eagletrt/fenice-bms-hv-sw/Schematics/BMS_HV-2017-2018 chimera/BMS_HV/MainBoard/V1/MainBoard.kicad_pcb

## KiCad design Schematics/BMS_HV-2017-2018 chimera/BMS_HV/MainBoard/V1/MainBoard.kicad_pcb (2018-10-10, an earlier design)

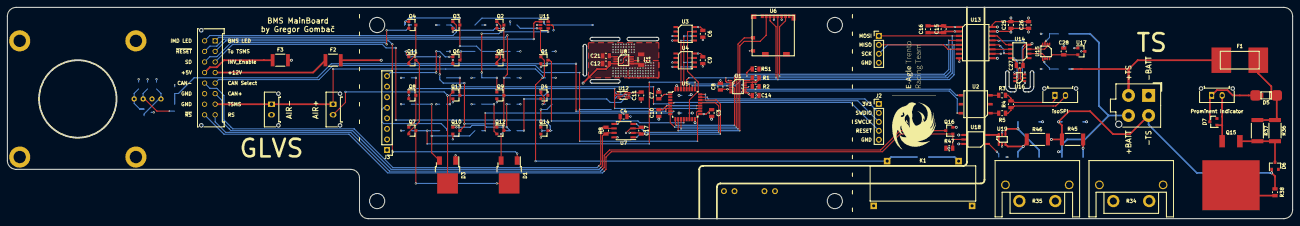
[picture p15: board MainBoard.kicad_pcb from above]

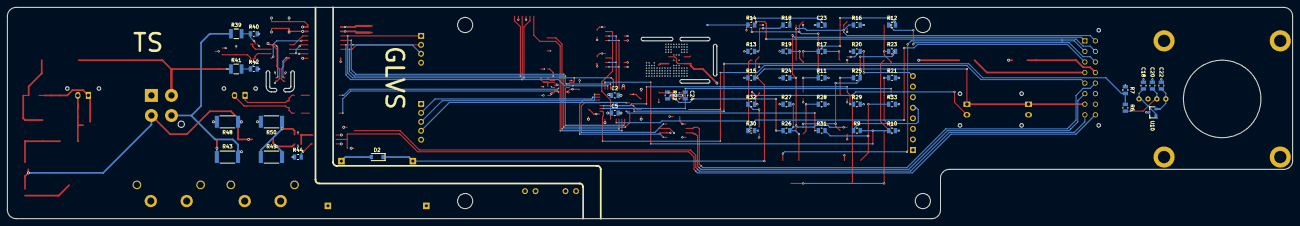
[picture p16: board MainBoard.kicad_pcb from below]

Board: 4 copper layers, 365.0 x 60.0 mm, 133 parts (45 on the bottom side), 98 nets.

Parts:
C1: 47u; C_1206_3216Metric
C2, C12: 4.7u; C_0805_2012Metric
C3, C4, C7, C11, C15, C17, C26, C28: 100n; C_0805_2012Metric
C5, C23, C27: 1u; C_0805_2012Metric
C6, C8, C9, C10, C14, C21, C24: 10n; C_0805_2012Metric
C16, C25: 10u; C_0805_2012Metric
C18, C22: 47n; C_0805_2012Metric
C20: 4.7n; C_0805_2012Metric
D1, D3: BT150S-600R; TO-252-2
D2: BAS16GW; D_SOD-123
D4, D6, D7: MMBZ4624; D_SOT-23_ANK
D5: BZD27C56P; DO-219AB
F1: 0885001.DR; SMD_Fuse
F2, F3: 0ZCG 2A; Fuse_1812_4532Metric
J1: isoSPI; Molex_Micro-Fit_3.0_43650-0215_1x02_P3.00mm_Vertical
J2: SWDebug; PinHeader_1x05_P2.54mm_Vertical
J3: IMD; PinHeader_1x08_P3mm_Vertical
J4: IO; Molex_Micro-Fit_3.0_43045-1612_2x08_P3.00mm_Vertical
J5: AIR-; Molex_Micro-Fit_3.0_43650-0215_1x02_P3.00mm_Vertical
J6: AIR+; Molex_Micro-Fit_3.0_43650-0215_1x02_P3.00mm_Vertical
J7: ProminentIndicator; Molex_Micro-Fit_3.0_43650-0215_1x02_P3.00mm_Vertical
J8: HV; Molex_Mega-Fit_76829-0104_2x02_P5.70mm_Vertical
J9: IMD_TS+; PinHeader_1x02_P3mm_Vertical
J10: IMD_TS-; PinHeader_1x02_P3mm_Vertical
K1: KT12-1A; KT_THT
Q1, Q5, Q6, Q12: TSM2306; SOT-23
Q2, Q3, Q4, Q7, Q9, Q10, Q11: TSM3401; SOT-23
Q8, Q13, Q16: TSM2312; SOT-23
Q14: BC846AW; SOT-23
Q15: BULB49D; D2PAK
R1: 604; R_0805_2012Metric
R2: 1.4K; R_0805_2012Metric
R3, R5: 22; R_0805_2012Metric
R4: 100; R_0805_2012Metric
R6, R7, R16, R17, R18, R19, R24, R25, R28: 10K; R_0805_2012Metric
R8: 120; R_0805_2012Metric
R9: 1.6K; R_0805_2012Metric
R10: 590; R_0805_2012Metric
R11, R14, R15, R21, R22, R27, R29, R33, R47: 100K; R_0805_2012Metric
R12, R23: 1M; R_0805_2012Metric
R13: 220K; R_0805_2012Metric
R20: 2K2; R_0805_2012Metric
R26, R31: 3.3K; R_0805_2012Metric
R30, R51: 1K; R_0805_2012Metric
R32: 22K; R_0805_2012Metric
R34, R35: 10K; TO-247_wHeatsink
R36, R37: 390K; R_2512_6332Metric
R38: 330; R_0805_2012Metric
R39, R41: 10M; R_1210_3225Metric
R40: 71K5; R_0805_2012Metric
R42: 34K8; R_0805_2012Metric
R43, R48: 100M; R_2512_6332Metric
R44: 470; R_0805_2012Metric
R45: 10M; R_2512_6332Metric
R46: 1G; R_2512_6332Metric
R49, R50: 2.2M; R_2512_6332Metric
U1: LTC6820; MSOP-16
U2: HM2103
U3, U4: M24M02; SON-8
U5: STM32F334K8; LQFP-32_7x7mm_P0.8mm
U6: MicroSD; Molex_MicroSD_PushPull
U7: MCP2562; SOIC-8_3.9x4.9mm_P1.27mm
U8: LP2989; SOIC-8
U9: HTFS200-P; HTFS 200-P
U10: REF2920; SOT-23
U11: MAX16053; SOT-23-6
U12: SN74LVC1G123; VSSOP-8_2.3x2mm_P0.5mm
U13: ISOW7841; SOIC-16
U14: LTC1865L; SON-8
U15: LTC6259; MSOP-8
U16: REF3433; SOT-23-6
U17: REF2940; SOT-23
U18: FODM611
U19: TPS3700; SOT-23-6

Connections:
+3V3: C1.1, C2.1, C3.1, C4.1, C5.1, C6.1, C7.1, C8.1, C9.1, C10.1, C11.1, C15.1, C16.1, J2.1, R14.1, R22.2, R51.2, U1.6, U3.8, U4.3, U4.8, U5.1, U5.5, U5.17, U6.4, U7.5, U8.5, U8.6, U12.3, U12.8, U13.1
+5V: C12.1, C14.1, C17.1, C18.1, F3.1, U1.9, U1.12, U7.3, U8.4, U8.8, U9.1, U10.1, U18.6
+12V: F2.2, J3.2, Q2.2, Q3.2, Q9.2, Q10.2, R11.1, R13.1, R16.2, R21.2, R24.2, R30.1, U11.5
+BATT: J8.4, K1.3, R39.2, R43.1
+TS: F1.1, J8.3, J9.1, J9.2, R34.2, R35.2, R41.2, R43.2, R45.1
-BATT: C25.2, C26.2, C27.2, C28.2, J8.1, R40.2, R42.2, R48.2, R50.1, U13.9, U13.15, U14.4, U15.4, U16.1, U16.2, U17.3, U19.2
-TS: D6.2, J8.2, J10.1, J10.2, R38.2, R45.2, R46.2, R48.1
/6820: U1.5, U5.9
/BMS_Fault: Q13.1, R29.1, U5.20
/CAN+: J4.6, R8.2, U7.7
/CAN-: J4.13, R8.1, U7.6
/CANS: J4.5, U5.18
/CD: U5.11, U6.9
/Current: C20.1, R6.1, U9.3
/HV/3V3ISO: C27.1, U14.8, U16.5, U16.6
/HV/4VISO: C28.1, U15.8, U17.2
/HV/5VISO: C25.1, C26.1, R44.1, U13.10, U13.16, U16.3, U16.4, U17.1, U19.5
/HV/PackV: U14.3, U15.1, U15.2
/HV/TSV: U14.2, U15.6, U15.7
/I+: U1.11, U2.4
/I-: U1.10, U2.6
/IBIAS: R1.2, U1.16
/ICMP: R1.1, R2.2, U1.15
/IMD: R9.2, R10.1, U5.25
/IMD_Fault: J3.8, Q6.1, R20.1
/MISO: R51.1, U1.3, U5.27, U6.7, U13.6
/MOSI: U1.2, U5.28, U6.3, U13.3
/PADC: U5.8, U13.4
/PC_Ended: R31.2, U5.7
/RST: J2.4, U5.4
/SCK: U1.4, U5.26, U6.5, U13.5
/SCL: U3.6, U4.6, U5.29
/SDA: U3.5, U4.5, U5.30
/SDCard: U5.10, U6.2
/SD_Status: Q1.3, U5.12
/SWCLK: J2.3, U5.24
/SWDIO: J2.2, U5.23
/Shutdown/BMS_SD: Q7.2, Q11.3
/Shutdown/IMD_SD: Q4.3, Q11.2, R23.2
/Shutdown/~RESET: Q2.1, Q9.1, R11.2, U11.4
/TS_ON: Q8.1, U5.19, U12.2
/WC: U3.7, U4.7, U5.14
/isoSPI+: J1.1, R3.1, R4.2
/isoSPI-: J1.2, R4.1, R5.1
BMS_LED: J4.1, Q9.3, Q10.1, Q12.3, R24.1
From_SD: J4.11, Q4.2, R12.2
From_TSMS: D2.1, J4.7, J5.1, J6.1, K1.1, Q1.1, R15.1
GND: C1.2, C2.2, C3.2, C4.2, C5.2, C6.2, C7.2, C8.2, C9.2, C10.2, C11.2, C12.2, C14.2, C15.2, C16.2, C17.2, C18.2, C20.2, C21.2, C22.2, C23.2, D2.2, D3.1, J2.5, J3.1, J3.3, J3.4, J4.14, J4.15, J5.2, K1.2, Q1.2, Q6.2, Q8.2, Q13.2, Q14.2, Q16.2, R2.1, R7.1, R10.2, R15.2, R18.2, R19.1, R20.2, R27.2, R28.1, R29.2, R33.2, R47.2, U1.1, U1.7, U1.8, U1.13, U1.14, U3.3, U3.4, U4.4, U5.16, U5.31, U5.32, U6.6, U6.10, U7.2, U7.8, U8.3, U9.2, U10.3, U11.2, U12.1, U12.4, U13.2, U13.8, U18.4
IMD_LED: J4.9, Q2.3, Q3.1, Q5.3, R16.1
INV_Enable: J4.3, Q14.3, R30.2
NRelayStat: J4.16, Q16.1, R47.1, U18.5
unnamed: C21.1, U8.1
unnamed: C22.1, U9.4, U10.2
unnamed: C23.1, U11.6
unnamed: C24.1, R22.1, U12.7
unnamed: C24.2, U12.6
unnamed: D1.2, Q7.3
unnamed: D1.3, R26.1, R27.1
unnamed: D3.2, D4.1, J6.2
unnamed: D3.3, R31.1, R33.1
unnamed: D4.2, R32.2
unnamed: D5.1, D7.1, J7.1
unnamed: D5.2, F1.2, R36.1, R37.1
unnamed: D6.1, Q15.1, R36.2, R37.2
unnamed: D7.2, J7.2, Q15.2
unnamed: F2.1, J4.4
unnamed: F3.2, J4.12
unnamed: J3.5, R9.1
unnamed: K1.4, R34.1, R35.1
unnamed: Q3.3, Q4.1, Q5.1, R12.1, R17.1
unnamed: Q5.2, R19.2
unnamed: Q6.3, R17.2
unnamed: Q7.1, Q8.3, R21.1
unnamed: Q10.3, Q11.1, Q12.1, R23.1, R25.1
unnamed: Q12.2, R28.2
unnamed: Q13.3, R25.2
unnamed: Q14.1, R32.1
unnamed: Q15.3, R38.1
unnamed: R3.2, U2.3
unnamed: R5.2, U2.1
unnamed: R6.2, R7.2, U5.6
unnamed: R13.2, R18.1, U11.3
unnamed: R26.2, U12.5
unnamed: R39.1, R40.1, U15.3
unnamed: R41.1, R42.1, U15.5
unnamed: R44.2, U18.1
unnamed: R46.1, R49.1, U19.3
unnamed: R49.2, R50.2, U19.4
unnamed: U5.21, U7.4
unnamed: U5.22, U7.1
unnamed: U13.11, U14.6
unnamed: U13.12, U14.7
unnamed: U13.13, U14.1
unnamed: U13.14, U14.5
unnamed: U18.3, U19.1, U19.6
RESET_BUTTON: J4.10, R14.2, U11.1
RelayStat: J4.8, Q16.3
To_TSMS: D1.1, J4.2
