eagletrt/fenice-bms-hv-sw/openblt_cellboard/Core/Inc/main.h

#define ADDRESS_2_Pin GPIO_PIN_1
#define ADDRESS_2_GPIO_Port GPIOA
#define ADDRESS_1_Pin GPIO_PIN_2
#define ADDRESS_1_GPIO_Port GPIOA
#define ADDRESS_0_Pin GPIO_PIN_3
#define ADDRESS_0_GPIO_Port GPIOA
#define LED_Pin GPIO_PIN_15
#define LED_GPIO_Port GPIOA
