eagletrt/fenice-bms-hv-sw/mainboard/Src/pack/current.c

/**
 * @file current.c
 * @brief Functions that handle current measurement
 *
 * @date Sep 24, 2021
 *
 * @author Matteo Bonora [matteo.bonora@studenti.unitn.it]
 * @author Federico Carbone [federico.carbone@studenti.unitn.it]
 * @author Antonio Gelain [antonio.gelain@studenti.unitn.it]
 */
#include "pack/current.h"

#include <math.h>
#include <stdbool.h>

#include "stm32f4xx_hal.h"
#include "mainboard_config.h"
#include "error_simple.h"

#define MEASURE_SAMPLE_SIZE 128

#define CURRENT_SENSITIVITY_LOW 40e-3f // V / A
#define CURRENT_SENSITIVITY_HIGH 6.67e-3f // V / A

#define CURRENT_DIVIDER_RATIO_INVERSE ((330.f + 169.f) / 330.f)

uint16_t adc_50[MEASURE_SAMPLE_SIZE]  = { 0 };
uint16_t adc_300[MEASURE_SAMPLE_SIZE] = { 0 };

current_t prev_current = 0.f, filtered_current = 0.f;
current_t current[CURRENT_SENSOR_NUM] = { 0.f };

current_t V0L = 0, V0H = 0;  // Voltage offset (Vout(0A))
current_t volt_300 = 0; // Voltage value of the Hall effect sensor

current_t _current_convert_low(float volt) {
    return (CURRENT_DIVIDER_RATIO_INVERSE / CURRENT_SENSITIVITY_LOW) * (volt - V0L);
}

current_t _current_convert_high(float volt) {
    return (CURRENT_DIVIDER_RATIO_INVERSE / CURRENT_SENSITIVITY_HIGH) * (volt - V0H);
}

#define CURRENT_SHUNT_VREF_OFFSET 0.454f // 0.9f
#define CURRENT_SHUNT_OP_GAIN 75.f
#define CURRENT_SHUNT_RESISTANCE 1e-4f

current_t _current_convert_shunt(float volt) {
    return (volt - CURRENT_SHUNT_VREF_OFFSET) / (CURRENT_SHUNT_OP_GAIN * CURRENT_SHUNT_RESISTANCE);
}

void current_start_measure() {
    HAL_ADC_Start_DMA(&ADC_HALL50, (uint32_t *)adc_50, MEASURE_SAMPLE_SIZE);
    HAL_ADC_Start_DMA(&ADC_HALL300, (uint32_t *)adc_300, MEASURE_SAMPLE_SIZE);
}


uint32_t current_read(float shunt_adc_val) {
    uint32_t time = HAL_GetTick();
    float avg_50 = 0;
    float avg_300 = 0;
    for (size_t i = 0; i < MEASURE_SAMPLE_SIZE; i++) {
        avg_50 += adc_50[i];
        avg_300 += adc_300[i];
    }

    // Convert Hall-low (50A)
    float volt = avg_50 * 3.3f / 4095.f / MEASURE_SAMPLE_SIZE;
    current[CURRENT_SENSOR_50] = _current_convert_low(volt);

    // Convert Hall-high (300A)
    volt_300 = avg_300 * 3.3f / 4095.f / MEASURE_SAMPLE_SIZE;
    current[CURRENT_SENSOR_300] = _current_convert_high(volt_300);

    // Convert Shunt
    current[CURRENT_SENSOR_SHUNT] = _current_convert_shunt(shunt_adc_val);

    // Filter current
    current_t hall_50 = fabsf(current[CURRENT_SENSOR_50]);
    current_t hall_300 = fabsf(current[CURRENT_SENSOR_300]);

    // Return current read from the correct
    if (hall_50 < 34 && hall_300 < 34)
        filtered_current = current[CURRENT_SENSOR_50];
    else
        filtered_current = current[CURRENT_SENSOR_300];
    // Filter current
    const float alpha = 0.4f;
    prev_current = filtered_current = alpha * prev_current + (1.f - alpha) * filtered_current;

    // Check for over-currents
    if (current_get_current() < CURRENT_MIN_THRESHOLD) {
        error_simple_set(ERROR_GROUP_ERROR_OVER_CURRENT, 0);
    } else {
        error_simple_reset(ERROR_GROUP_ERROR_OVER_CURRENT, 0);
    }

    if (current_get_current() > CURRENT_MAX_THRESHOLD) {
        error_simple_set(ERROR_GROUP_ERROR_OVER_CURRENT, 0);
    } else {
        error_simple_reset(ERROR_GROUP_ERROR_OVER_CURRENT, 0);
    }
    return time;
}

void current_zero() {
    uint32_t avg_50  = 0;
    uint32_t avg_300 = 0;
    for (size_t i = 0; i < MEASURE_SAMPLE_SIZE; ++i) {
        avg_50 += adc_50[i];
        avg_300 += adc_300[i];
    }
    V0L = avg_50 * (3.3f / 4095 / MEASURE_SAMPLE_SIZE);
    V0H = avg_300 * (3.3f / 4095 / MEASURE_SAMPLE_SIZE);
}

current_t current_get_current() {
    return filtered_current;
}
current_t * current_get_current_sensors() {
    return current;
}

current_t current_get_current_from_sensor(uint8_t sensor) {
    if (sensor >= CURRENT_SENSOR_NUM)
        return 0;
    return current[sensor];
}

void current_check_errors() {
    current_t hall_300 = current[CURRENT_SENSOR_300];
    if (hall_300 < CURRENT_MIN_THRESHOLD) {
        error_simple_set(ERROR_GROUP_ERROR_OVER_CURRENT, 0);
    } else {
        error_simple_reset(ERROR_GROUP_ERROR_OVER_CURRENT, 0);
    }

    if (hall_300 > CURRENT_MAX_THRESHOLD) {
        error_simple_set(ERROR_GROUP_ERROR_OVER_CURRENT, 0);
    } else {
        error_simple_reset(ERROR_GROUP_ERROR_OVER_CURRENT, 0);
    }
    
    // Hall effect sensor disconnected
    if (volt_300 < CURRENT_SENSOR_DISCONNECTED_THRESHOLD) {
        // error_simple_set(ERROR_GROUP_ERROR_CONNECTOR_DISCONNECTED, 1);
    } else {
        error_simple_reset(ERROR_GROUP_ERROR_CONNECTOR_DISCONNECTED, 1);
    }
}
