eagletrt/fenice-bms-hv-sw/openblt_cellboard/Core/Inc/BLT/blt_conf.h

/************************************************************************************//**
* \file         Demo/ARMCM4_STM32F4_Nucleo_F429ZI_GCC/Boot/blt_conf.h
* \brief        Bootloader configuration header file.
* \ingroup      Boot_ARMCM4_STM32F4_Nucleo_F429ZI_GCC
* \internal
*----------------------------------------------------------------------------------------
*                          C O P Y R I G H T
*----------------------------------------------------------------------------------------
*   Copyright (c) 2021  by Feaser    http://www.feaser.com    All rights reserved
*
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
* OpenBLT is distributed in the hope that it will be useful, but WITHOUT ANY WARRANTY;
* without even the implied warranty of MERCHANTABILITY or FITNESS FOR A PARTICULAR
* PURPOSE. See the GNU General Public License for more details.
*
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
* \endinternal
****************************************************************************************/
#ifndef BLT_CONF_H
#define BLT_CONF_H

#include "main.h"

/****************************************************************************************
*   C P U   D R I V E R   C O N F I G U R A T I O N
****************************************************************************************/
/* To properly initialize the baudrate clocks of the communication interface, typically
 * the speed of the crystal oscillator and/or the speed at which the system runs is
 * needed. Set these through configurables BOOT_CPU_XTAL_SPEED_KHZ and
 * BOOT_CPU_SYSTEM_SPEED_KHZ, respectively. To enable data exchange with the host that is
 * not dependent on the targets architecture, the byte ordering needs to be known.
 * Setting BOOT_CPU_BYTE_ORDER_MOTOROLA to 1 selects big endian mode and 0 selects
 * little endian mode.
 *
 * Set BOOT_CPU_USER_PROGRAM_START_HOOK to 1 if you would like a hook function to be
 * called the moment the user program is about to be started. This could be used to
 * de-initialize application specific parts, for example to stop blinking an LED, etc.
 */
/** \brief Frequency of the external crystal oscillator. */
#define BOOT_CPU_XTAL_SPEED_KHZ          (20000)
/** \brief Desired system speed. */
#define BOOT_CPU_SYSTEM_SPEED_KHZ        (80000)
/** \brief Motorola or Intel style byte ordering. */
#define BOOT_CPU_BYTE_ORDER_MOTOROLA     (0)
/** \brief Enable/disable hook function call right before user program start. */
#define BOOT_CPU_USER_PROGRAM_START_HOOK (0)


/****************************************************************************************
*   C O M M U N I C A T I O N   I N T E R F A C E   C O N F I G U R A T I O N
****************************************************************************************/
/* The NET communication interface for firmware updates via TCP/IP is selected by setting
 * the BOOT_COM_NET_ENABLE configurable to 1. The maximum amount of data bytes in a
 * message for data transmission and reception is set through BOOT_COM_NET_TX_MAX_DATA
 * and BOOT_COM_NET_RX_MAX_DATA, respectively. The default IP address is configured
 * with the macros BOOT_COM_NET_IPADDRx. The default netmask is configured with the
 * macro BOOT_COM_NET_NETMASKx. The default gateway is configured with the macros
 * BOOT_COM_NET_GATEWAYx. The bootloader acts and a TCP/IP server. The port the server
 * listen on for connections is configured with BOOT_COM_NET_PORT.
 * In case the network switch/router supports a DHCP server, you can set configuration
 * macro BOOT_COM_NET_DHCP_ENABLE to 1 to enable the DHCP client. In this case the
 * DHCP client handles the automatic IP address assignment. In this case the macros for
 * configuring the IP address, network mask and gateway address are no longer needed.
 */
/** \brief Enable/disable the NET transport layer. */
#define BOOT_COM_NET_ENABLE               (0)
/** \brief Configure number of bytes in the target->host data packet. */
#define BOOT_COM_NET_TX_MAX_DATA          (64)
/** \brief Configure number of bytes in the host->target data packet. */
#define BOOT_COM_NET_RX_MAX_DATA          (64)
/** \brief Configure the port that the TCP/IP server listens on */
#define BOOT_COM_NET_PORT                 (1000)
/** \brief Enable/disable DHCP client for automatically obtaining an IP address. */
#define BOOT_COM_NET_DHCP_ENABLE          (1)
/** \brief Configure the 1st byte of the IP address */
#define BOOT_COM_NET_IPADDR0              (192)
/** \brief Configure the 2nd byte of the IP address */
#define BOOT_COM_NET_IPADDR1              (168)
/** \brief Configure the 3rd byte of the IP address */
#define BOOT_COM_NET_IPADDR2              (178)
/** \brief Configure the 4th byte of the IP address */
#define BOOT_COM_NET_IPADDR3              (50)
/** \brief Configure the 1st byte of the network mask */
#define BOOT_COM_NET_NETMASK0             (255)
/** \brief Configure the 2nd byte of the network mask */
#define BOOT_COM_NET_NETMASK1             (255)
/** \brief Configure the 3rd byte of the network mask */
#define BOOT_COM_NET_NETMASK2             (255)
/** \brief Configure the 4th byte of the network mask */
#define BOOT_COM_NET_NETMASK3             (0)
/** \brief Configure the 1st byte of the gateway address */
#define BOOT_COM_NET_GATEWAY0             (192)
/** \brief Configure the 2nd byte of the gateway address */
#define BOOT_COM_NET_GATEWAY1             (168)
/** \brief Configure the 3rd byte of the gateway address */
#define BOOT_COM_NET_GATEWAY2             (178)
/** \brief Configure the 4th byte of the gateway address */
#define BOOT_COM_NET_GATEWAY3             (1)
/** \brief Enable/disable the deferred initialization mechanism. When enabled, the
 *         communication interface is only initialized when: (a) no valid user program
 *         is detected, or (b) when CpuUserProgramStartHook() returns BLT_FALSE. Your
 *         bootloader application can explicitly initialize the communication interface
 *         by calling ComDeferredInit().
 */
#define BOOT_COM_NET_DEFERRED_INIT_ENABLE (1)

/* The USB communication interface is selected by setting the BOOT_COM_USB_ENABLE
 * configurable to 1. The maximum amount of data bytes in a message for data transmission
 * and reception is set through BOOT_COM_USB_TX_MAX_DATA and BOOT_COM_USB_RX_MAX_DATA,
 * respectively.
 *
 */
/** \brief Enable/disable USB transport layer. */
#define BOOT_COM_USB_ENABLE             (0)
/** \brief Configure number of bytes in the target->host data packet. */
#define BOOT_COM_USB_TX_MAX_DATA        (63)
/** \brief Configure number of bytes in the host->target data packet. */
#define BOOT_COM_USB_RX_MAX_DATA        (63)

/* The CAN communication interface is selected by setting the BOOT_COM_CAN_ENABLE
 * configurable to 1. Configurable BOOT_COM_CAN_BAUDRATE selects the communication speed
 * in bits/second. Two CAN messages are reserved for communication with the host. The
 * message identifier for sending data from the target to the host is configured with
 * BOOT_COM_CAN_TXMSG_ID. The one for receiving data from the host is configured with
 * BOOT_COM_CAN_RXMSG_ID. Note that an extended 29-bit CAN identifier is configured by
 * OR-ing with mask 0x80000000. The maximum amount of data bytes in a message for data
 * transmission and reception is set through BOOT_COM_CAN_TX_MAX_DATA and
 * BOOT_COM_CAN_RX_MAX_DATA, respectively. It is common for a microcontroller to have more
 * than 1 CAN controller on board. The zero-based BOOT_COM_CAN_CHANNEL_INDEX selects the
 * CAN controller channel.
 *
 */
/** \brief Enable/disable CAN transport layer. */
#define BOOT_COM_CAN_ENABLE             (1)
/** \brief Configure the desired CAN baudrate. */
#define BOOT_COM_CAN_BAUDRATE           (1000000)
/** \brief Configure CAN message ID target->host. */
#define BOOT_COM_CAN_TX_MSG_ID          (0x04 + 2 * (HAL_GPIO_ReadPin(ADDRESS_2_GPIO_Port, ADDRESS_2_Pin) | HAL_GPIO_ReadPin(ADDRESS_1_GPIO_Port, ADDRESS_1_Pin) << 1 | HAL_GPIO_ReadPin(ADDRESS_0_GPIO_Port, ADDRESS_0_Pin) << 2))
/** \brief Configure number of bytes in the target->host CAN message. */
#define BOOT_COM_CAN_TX_MAX_DATA        (8)
/** \brief Configure CAN message ID host->target. */
#define BOOT_COM_CAN_RX_MSG_ID          (0x05 + 2 * (HAL_GPIO_ReadPin(ADDRESS_2_GPIO_Port, ADDRESS_2_Pin) | HAL_GPIO_ReadPin(ADDRESS_1_GPIO_Port, ADDRESS_1_Pin) << 1 | HAL_GPIO_ReadPin(ADDRESS_0_GPIO_Port, ADDRESS_0_Pin) << 2))
/** \brief Configure number of bytes in the host->target CAN message. */
#define BOOT_COM_CAN_RX_MAX_DATA        (8)
/** \brief Select the desired CAN peripheral as a zero based index. */
#define BOOT_COM_CAN_CHANNEL_INDEX      (0)

/* The RS232 communication interface is selected by setting the BOOT_COM_RS232_ENABLE
 * configurable to 1. Configurable BOOT_COM_RS232_BAUDRATE selects the communication speed
 * in bits/second. The maximum amount of data bytes in a message for data transmission
 * and reception is set through BOOT_COM_RS232_TX_MAX_DATA and BOOT_COM_RS232_RX_MAX_DATA,
 * respectively. It is common for a microcontroller to have more than 1 UART interface
 * on board. The zero-based BOOT_COM_RS232_CHANNEL_INDEX selects the UART interface.
 *
 */
/** \brief Enable/disable UART transport layer. */
#define BOOT_COM_RS232_ENABLE            (0)
/** \brief Configure the desired communication speed. */
#define BOOT_COM_RS232_BAUDRATE          (57600)
/** \brief Configure number of bytes in the target->host data packet. */
#define BOOT_COM_RS232_TX_MAX_DATA       (64)
/** \brief Configure number of bytes in the host->target data packet. */
#define BOOT_COM_RS232_RX_MAX_DATA       (64)
/** \brief Select the desired UART peripheral as a zero based index. */
#define BOOT_COM_RS232_CHANNEL_INDEX     (2)


/****************************************************************************************
*   B A C K D O O R   E N T R Y   C O N F I G U R A T I O N
****************************************************************************************/
/* It is possible to implement an application specific method to force the bootloader to
 * stay active after a reset. Such a backdoor entry into the bootloader is desired in
 * situations where the user program does not run properly and therefore cannot
 * reactivate the bootloader. By enabling these hook functions, the application can
 * implement the backdoor, which overrides the default backdoor entry that is programmed
 * into the bootloader. When desired for security purposes, these hook functions can
 * also be implemented in a way that disables the backdoor entry altogether.
 */
/** \brief Enable/disable the backdoor override hook functions. */
#define BOOT_BACKDOOR_HOOKS_ENABLE      (0)

/** \brief Backdoor timeout before starting user program */
#define BOOT_BACKDOOR_ENTRY_TIMEOUT_MS (1000)

/****************************************************************************************
*   N O N - V O L A T I L E   M E M O R Y   D R I V E R   C O N F I G U R A T I O N
****************************************************************************************/
/* The NVM driver typically supports erase and program operations of the internal memory
 * present on the microcontroller. Through these hook functions the NVM driver can be
 * extended to support additional memory types such as external flash memory and serial
 * eeproms. The size of the internal memory in kilobytes is specified with configurable
 * BOOT_NVM_SIZE_KB. If desired the internal checksum writing and verification method can
 * be overridden with a application specific method by enabling configuration switch
 * BOOT_NVM_CHECKSUM_HOOKS_ENABLE.
 */
/** \brief Enable/disable the NVM hook function for supporting additional memory devices. */
#define BOOT_NVM_HOOKS_ENABLE           (0)
/** \brief Configure the size of the default memory device (typically flash EEPROM). */
#define BOOT_NVM_SIZE_KB                (128)
/** \brief Enable/disable hooks functions to override the user program checksum handling. */
#define BOOT_NVM_CHECKSUM_HOOKS_ENABLE  (0)


/****************************************************************************************
*   F L A S H   M E M O R Y   D R I V E R   C O N F I G U R A T I O N
****************************************************************************************/
/** \brief This microcontroller has a larger vector table then the default STM32F7xx
 *         project as assumed in the bootloader's core. This means the user program has
 *         a different checksum location, because this one is added at the end of the
 *         user program's vector table.
 */
#define BOOT_FLASH_VECTOR_TABLE_CS_OFFSET (0x194)


/****************************************************************************************
*   W A T C H D O G   D R I V E R   C O N F I G U R A T I O N
****************************************************************************************/
/* The COP driver cannot be configured internally in the bootloader, because its use
 * and configuration is application specific. The bootloader does need to service the
 * watchdog in case it is used. When the application requires the use of a watchdog,
 * set BOOT_COP_HOOKS_ENABLE to be able to initialize and service the watchdog through
 * hook functions.
 */
/** \brief Enable/disable the hook functions for controlling the watchdog. */
#define BOOT_COP_HOOKS_ENABLE           (0)


/****************************************************************************************
*   S E E D / K E Y   S E C U R I T Y   C O N F I G U R A T I O N
****************************************************************************************/
/* A security mechanism can be enabled in the bootloader's XCP module by setting configu-
 * rable BOOT_XCP_SEED_KEY_ENABLE to 1. Before any memory erase or programming
 * operations can be performed, access to this resource need to be unlocked.
 * In the Microboot settings on tab "XCP Protection" you need to specify a DLL that
 * implements the unlocking algorithm. The demo programs are configured for the (simple)
 * algorithm in "libseednkey.dll". The source code for this DLL is available so it can be
 * customized to your needs.
 * During the unlock sequence, Microboot requests a seed from the bootloader, which is in
 * the format of a byte array. Using this seed the unlock algorithm in the DLL computes
 * a key, which is also a byte array, and sends this back to the bootloader. The
 * bootloader then verifies this key to determine if programming and erase operations are
 * permitted.
 * After enabling this feature the hook functions XcpGetSeedHook() and XcpVerifyKeyHook()
 * are called by the bootloader to obtain the seed and to verify the key, respectively.
 */
#define BOOT_XCP_SEED_KEY_ENABLE        (0)


#endif /* BLT_CONF_H */
/*********************************** end of blt_conf.h *********************************/
