eagletrt/fenice-bms-hv-sw/src/bms/Src/ltc6813.c

/**
 * @file		ltc6813.c
 * @brief		This file contains the functions to communicate with the LTCs
 *
 * @date		Oct 08, 2019
 * @author	Matteo Bonora [matteo.bonora@studenti.unitn.it]
 */

#include "ltc6813.h"

// Set to 1 to emulate the LTC daisy chain
#define LTC6813_EMU 0

/**
 * @brief		Polls all the registers of the LTC6813 and updates the cell
 * array
 * @details	It executes multiple rdcv requests to the LTCs and saves the values
 * 					in the voltage variable of the CELL_Ts.
 *
 * 					1     CMD0    8     CMD1      16      32
 * 					|- - - - - - -|- - - - - - - -|- ... -|
 * 					1 0 0 0 0 0 0 0 0 0 0 0 X X X X  PEC
 * 					 Address |             |  Reg  |
 * 					  (BRD)
 *
 * @param		spi		The SPI configuration structure
 * @param		ltc		The array of LTC6813 configurations
 * @param		volts	The array of voltages
 * @param		error	The error return value
 */
uint8_t ltc6813_read_voltages(SPI_HandleTypeDef *spi, LTC6813_T ltc[],
							  uint16_t volts[], ERROR_STATUS_T volts_error[],
							  WARNING_T *warning, ERROR_T *error) {
	uint8_t cmd[4];
	uint16_t cmd_pec;
	uint8_t data[8];

	cmd[0] = 0;  // Broadcast

	uint8_t count = 0;  // volts[] index
	for (uint8_t reg = 0; reg < LTC6813_REG_COUNT; reg++) {
		cmd[1] = (uint8_t)rdcv_cmd[reg];
		cmd_pec = _pec15(2, cmd);
		cmd[2] = (uint8_t)(cmd_pec >> 8);
		cmd[3] = (uint8_t)(cmd_pec);

		_wakeup_idle(spi, false);

		HAL_GPIO_WritePin(CS_LTC_GPIO_Port, CS_LTC_Pin, GPIO_PIN_RESET);
		if (HAL_SPI_Transmit(spi, cmd, 4, 100) != HAL_OK) {
			// goto End;
		}
		HAL_SPI_Receive(spi, data, 8 * LTC6813_COUNT, 100);
		HAL_GPIO_WritePin(CS_LTC_GPIO_Port, CS_LTC_Pin, GPIO_PIN_SET);

#if LTC6813_EMU > 0
		// Writes 3.6v to each cell

		uint8_t emu_i;
		for (emu_i = 0; emu_i < LTC6813_REG_CELL_COUNT * 2; emu_i++) {
			// 36000
			data[emu_i] = 0b10100000;
			data[++emu_i] = 0b10001100;
		}
		uint16_t emu_pec = _pec15(6, data);
		data[6] = (uint8_t)(emu_pec >> 8);
		data[7] = (uint8_t)emu_pec;
#endif

		if (_pec15(6, data) == (uint16_t)(data[6] * 256 + data[7])) {
			error_unset(ERROR_LTC_PEC_ERROR, &ltc->error);

			// For every cell in the register
			for (uint8_t cell = 0; cell < LTC6813_REG_CELL_COUNT; cell++) {
				volts[count] = _convert_voltage(&data[2 * cell]);

				ltc6813_check_voltage(volts[count], &volts_error[count],
									  warning, error);
				ER_CHK(error);
				count++;
			}
		} else {
			error_set(ERROR_LTC_PEC_ERROR, &ltc->error, HAL_GetTick());
		}

		*error = error_check_fatal(&ltc->error, HAL_GetTick());
		ER_CHK(error);
	}

End:;
	return count;
}

/**
 * @brief		Starts the LTC6813 ADC voltage conversion
 * @details	According to the datasheet, this command should take 2,335µs.
 * 					ADCV Command syntax:
 *
 * 					1     CMD0    8     CMD1      16      32
 * 					|- - - - - - -|- - - - - - - -|- ... -|
 * 					0 0 0 0 0 0 1 1 0 1 1 X 0 0 0 0  PEC
 * 					 Address |    | |     |
 * 					  (BRD)      Speed   DCP
 *
 * @param		spi		The spi configuration structure
 * @param		dcp		false to read voltages; true to read temperatures
 */
void _ltc6813_adcv(SPI_HandleTypeDef *spi, bool dcp) {
	uint8_t cmd[4];
	uint16_t cmd_pec;
	cmd[0] = (uint8_t)0b00000011;
	cmd[1] = (uint8_t)0b01100000 + dcp * 0b00010000;
	cmd_pec = _pec15(2, cmd);
	cmd[2] = (uint8_t)(cmd_pec >> 8);
	cmd[3] = (uint8_t)(cmd_pec);

	_wakeup_idle(spi, false);
	HAL_GPIO_WritePin(CS_LTC_GPIO_Port, CS_LTC_Pin, GPIO_PIN_RESET);
	HAL_SPI_Transmit(spi, cmd, 4, 100);
	HAL_Delay(1);
	HAL_GPIO_WritePin(CS_LTC_GPIO_Port, CS_LTC_Pin, GPIO_PIN_SET);
}

/**
 * @brief		Enable or disable the temperature measurement through
 *balancing
 * @details	Since it's not possible to read the temperatures from adiacent
 * 					cells at the same time, We split the measurement into
 *two times, read odd cells, and then even ones. To write configuration you
 *have to send 2 consecutive commands:
 *
 *					WRCFG:
 * 					1     CMD0    8     CMD1      16      32
 * 					|- - - - - - -|- - - - - - - -|- ... -|
 * 					0 0 0 0 0 0 0 0 0 0 0 0 0 0 0 1  PEC
 *
 *					CFGR:
 * 					1             8               16
 * 					|- - - - - - -|- - - - - - - -|
 * 					0 0 0 0 0 0 0 0 0 0 0 0 0 0 0 0
 * 					17            24              32
 * 					|- - - - - - -|- - - - - - - -|
 * 					0 0 0 0 0 0 0 0 0 0 0 0 0 0 0 0
 *					33            40              48      64
 *					|- - - - - - -|- - - - - - - -|- ... -|
 *					1 0 0 1 0 1 0 1 0 0 0 0 0 0 1 0  PEC	<- For odd cells
 *					              or
 *					0 1 0 0 1 0 1 0 0 0 0 0 0 0 0 1  PEC	<- For even
 *cells
 *
 * @param		hspi			The SPI configuration structure
 * @param		start_bal	whether to start temperature measurement
 * @param		even			Indicates whether we're reading odd or even
 *cells
 */
// TODO: remove this function
void _ltc6813_wrcfg(SPI_HandleTypeDef *hspi, bool start_bal, bool even) {
	uint8_t wrcfg[4];
	uint8_t cfgr[8];

	uint16_t cmd_pec;

	wrcfg[0] = 0x00;
	wrcfg[1] = 0x01;
	cmd_pec = _pec15(2, wrcfg);
	wrcfg[2] = (uint8_t)(cmd_pec >> 8);
	wrcfg[3] = (uint8_t)(cmd_pec);

	cfgr[0] = 0x00;
	cfgr[1] = 0x00;
	cfgr[2] = 0x00;
	cfgr[3] = 0x00;

	if (start_bal) {
		if (even) {
			// Command to balance cells (in order) 8,5,3,1 and 10
			cfgr[4] = 0b10010101;
			cfgr[5] = 0b00000010;
		} else {
			// Command to balance cells (in order) 7,4,2 and 9
			cfgr[4] = 0b01001010;
			// First 4 bits are for DCT0 and should remain 0
			cfgr[5] = 0b00000001;
		}
	} else {
		cfgr[4] = 0x00;
		cfgr[5] = 0x00;
	}
	cmd_pec = _pec15(6, cfgr);
	cfgr[6] = (uint8_t)(cmd_pec >> 8);
	cfgr[7] = (uint8_t)(cmd_pec);

	_wakeup_idle(hspi, true);

	HAL_GPIO_WritePin(CS_LTC_GPIO_Port, CS_LTC_Pin, GPIO_PIN_RESET);
	HAL_SPI_Transmit(hspi, wrcfg, 4, 100);
	HAL_Delay(1);
	HAL_SPI_Transmit(hspi, cfgr, 8, 100);
	HAL_Delay(1);
	HAL_GPIO_WritePin(CS_LTC_GPIO_Port, CS_LTC_Pin, GPIO_PIN_SET);

	// TODO: remove this
	_ltc6813_adcv(hspi, start_bal);
}

/**
 * @brief		This function is used to fetch the temperatures.
 * @details	The workings of this function are very similar to read_voltages,
 * 					the main difference to it is the presence of the even
 * 					parameter. Refer to the ltc6813_read_voltages comment for
 * 					the actual messages.
 *
 * @param		hspi		The SPI configuration structure
 * @param		even		indicates which set of cells is currently being
 * 									balanced: false for odd and true for even
 * cells
 * @param		ltc			The array of LTC6813 configurations
 * @param		temps		The array of temperatures
 * @param		error		The error return value
 */
uint8_t ltc6813_read_temperatures(SPI_HandleTypeDef *hspi, LTC6813_T *ltc,
								  uint16_t temps[],
								  ERROR_STATUS_T temps_error[],
								  ERROR_T *error) {
	uint8_t cmd[4];
	uint16_t cmd_pec;
	uint8_t data[8];

	cmd[0] = (uint8_t)0x80 + ltc->address;

	uint8_t count = 0;
	for (uint8_t reg = 0; reg < LTC6813_REG_COUNT; reg++) {
		cmd[1] = (uint8_t)rdcv_cmd[reg];
		cmd_pec = _pec15(2, cmd);
		cmd[2] = (uint8_t)(cmd_pec >> 8);
		cmd[3] = (uint8_t)(cmd_pec);

		_wakeup_idle(hspi, false);

		HAL_GPIO_WritePin(CS_LTC_GPIO_Port, CS_LTC_Pin, GPIO_PIN_RESET);
		HAL_Delay(1);
		HAL_SPI_Transmit(hspi, cmd, 4, 100);

		HAL_SPI_Receive(hspi, data, 8, 100);
		HAL_Delay(1);
		HAL_GPIO_WritePin(CS_LTC_GPIO_Port, CS_LTC_Pin, GPIO_PIN_SET);

#if LTC6813_EMU > 0
		// Writes 0.9292v (18°C) to each sensor

		for (uint8_t emu_i = 0; emu_i < LTC6813_REG_CELL_COUNT * 2; emu_i++) {
			// 9292
			data[emu_i] = 0b00100100;
			data[++emu_i] = 0b01001100;
		}
		uint16_t emu_pec = _pec15(6, data);
		data[6] = (uint8_t)(emu_pec >> 8);
		data[7] = (uint8_t)emu_pec;
#endif

		if (_pec15(6, data) == (uint16_t)(data[6] * 256 + data[7])) {
			error_unset(ERROR_LTC_PEC_ERROR, &ltc->error);

			// Counts the cell inside the register
			for (uint8_t cell = 0; cell < LTC6813_REG_CELL_COUNT; cell++) {
				uint16_t temp =
					_convert_temp(_convert_voltage(&data[2 * cell]));

				if (temp > 0) {
					temps[count] = temp;

					ltc6813_check_temperature(temps[count], &temps_error[count],
											  error);
					ER_CHK(error);
				}

				count++;
			}
		} else {
			error_set(ERROR_LTC_PEC_ERROR, &ltc->error, HAL_GetTick());
		}
	}

	*error = error_check_fatal(&ltc->error, HAL_GetTick());
	ER_CHK(error);  // In case of error, set the error and goto label End

End:;

	return count;
}

void ltc6813_wrcfg(SPI_HandleTypeDef *hspi, bool is_a,
				   uint8_t cfgr[LTC6813_COUNT][8]) {
	uint8_t cmd[4] = {0};

	if (is_a) {
		// WRCFGA
		cmd[1] = 1;
	} else {
		// WRCFGB
		cmd[1] = 0b00100100;
	}

	uint16_t cmd_pec = _pec15(2, cmd);
	cmd[2] = (uint8_t)(cmd_pec >> 8);
	cmd[3] = (uint8_t)(cmd_pec);

	HAL_GPIO_WritePin(CS_LTC_GPIO_Port, CS_LTC_Pin, GPIO_PIN_RESET);
	HAL_SPI_Transmit(hspi, cmd, 4, 100);
	HAL_Delay(1);

	for (uint8_t i = 0; i < LTC6813_COUNT; i++) {
		HAL_SPI_Transmit(hspi, cfgr[i], 8, 100);
	}

	HAL_GPIO_WritePin(CS_LTC_GPIO_Port, CS_LTC_Pin, GPIO_PIN_SET);
}

void _set_dcc(uint8_t indexes[], uint8_t cfgar[8], uint8_t cfgbr[8]) {
	for (uint8_t i = 0; i < PACK_MODULE_COUNT; i++) {
		if (indexes[i] < 8) {
			cfgar[4] += dcc[indexes[i]];
		} else if (indexes[i] >= 8 && indexes[i] < 12) {
			cfgar[5] += dcc[indexes[i]];
		} else if (indexes[i] >= 12 && indexes[i] < 16) {
			cfgbr[0] += dcc[indexes[i]];
		} else if (indexes[i] >= 16 && indexes[i] < 18) {
			cfgbr[1] += dcc[indexes[i]];
		}

		uint16_t pec = _pec15(6, cfgar);
		cfgar[6] = (uint8_t)(pec >> 8);
		cfgar[7] = (uint8_t)(pec);

		pec = _pec15(6, cfgbr);
		cfgbr[6] = (uint8_t)(pec >> 8);
		cfgbr[7] = (uint8_t)(pec);
	}
}

void ltc6813_set_balancing(SPI_HandleTypeDef *hspi, uint8_t *indexes,
						   int dcto) {
	uint8_t cfgar[LTC6813_COUNT][8] = {0};
	uint8_t cfgbr[LTC6813_COUNT][8] = {0};

	for (uint8_t i = 0; i < LTC6813_COUNT; i++) {
		// cfgbr[i][1] += 0b00001000; // set DTMEN
		cfgar[i][0] += 0b00000010;  // set DTEN
		cfgar[i][5] += dcto << 4;   // Set timer

		// For each LTC we set the correct cfgr
		_set_dcc(indexes, cfgar[i], cfgbr[i]);
	}
	_wakeup_idle(hspi, true);

	ltc6813_wrcfg(hspi, true, cfgar);
	ltc6813_wrcfg(hspi, false, cfgbr);
}

void ltc6813_wrcomm_i2c(SPI_HandleTypeDef *hspi, uint8_t data[1]) {
	uint8_t cmd[4] = {0b00000111, 0b00100001};  // WRCOMM

	uint16_t cmd_pec = _pec15(2, cmd);
	cmd[2] = (uint8_t)(cmd_pec >> 8);
	cmd[3] = (uint8_t)(cmd_pec);

	uint8_t comm[8];
	comm[0] = I2C_START & (data[0] >> 4);
	comm[1] = (data[0] << 4) & I2C_MASTER_ACK;

	comm[2] = I2C_BLANK & (data[1] >> 4);
	comm[3] = (data[1] << 4) & I2C_MASTER_ACK;

	comm[4] = I2C_STOP & (data[2] >> 4);
	comm[5] = (data[2] << 4) & I2C_MASTER_ACK;

	uint16_t pec = _pec15(6, comm);
	comm[6] = (uint8_t)(pec >> 8);
	comm[7] = (uint8_t)(pec);

	HAL_GPIO_WritePin(CS_LTC_GPIO_Port, CS_LTC_Pin, GPIO_PIN_RESET);
	HAL_SPI_Transmit(hspi, cmd, 4, 100);
	HAL_Delay(1);

	HAL_SPI_Transmit(hspi, comm, 8, 100);

	HAL_GPIO_WritePin(CS_LTC_GPIO_Port, CS_LTC_Pin, GPIO_PIN_SET);
}

void ltc6813_stcomm_i2c(SPI_HandleTypeDef *hspi) {
	uint8_t cmd[4] = {0};  // WRCOMM

	cmd[0] = 0b00000111;
	cmd[1] = 0b00100011;

	uint16_t cmd_pec = _pec15(2, cmd);
	cmd[2] = (uint8_t)(cmd_pec >> 8);
	cmd[3] = (uint8_t)(cmd_pec);

	HAL_GPIO_WritePin(CS_LTC_GPIO_Port, CS_LTC_Pin, GPIO_PIN_RESET);
	HAL_SPI_Transmit(hspi, cmd, 4, 100);
	HAL_SPI_Receive(hspi, NULL, 3 * 8 * 3, 200);
	HAL_GPIO_WritePin(CS_LTC_GPIO_Port, CS_LTC_Pin, GPIO_PIN_SET);
}

/**
 * @brief		Checks that voltage is between its thresholds.
 *
 * @param		volts		The voltage
 * @param		error		The error return code
 */
void ltc6813_check_voltage(uint16_t volts, ERROR_STATUS_T *volt_error,
						   WARNING_T *warning, ERROR_T *error) {
	if (volts < CELL_WARN_VOLTAGE) {
		*warning = WARN_CELL_LOW_VOLTAGE;
	}

	if (volts < CELL_MIN_VOLTAGE) {
		error_set(ERROR_CELL_UNDER_VOLTAGE, volt_error, HAL_GetTick());
	} else {
		error_unset(ERROR_CELL_UNDER_VOLTAGE, volt_error);
	}

	if (volts > CELL_MAX_VOLTAGE) {
		error_set(ERROR_CELL_OVER_VOLTAGE, volt_error, HAL_GetTick());
	} else {
		error_unset(ERROR_CELL_OVER_VOLTAGE, volt_error);
	}

	*error = error_check_fatal(volt_error, HAL_GetTick());
	ER_CHK(error);

End:;
}

/**
 * @brief		Checks that temperature is between its thresholds.
 *
 * @param		temp		The temperature
 * @param		error		The error return code
 */
void ltc6813_check_temperature(uint16_t temps, ERROR_STATUS_T *temp_error,
							   ERROR_T *error) {
	if (temps >= CELL_MAX_TEMPERATURE) {
		error_set(ERROR_CELL_OVER_TEMPERATURE, temp_error, HAL_GetTick());
	} else {
		error_unset(ERROR_CELL_OVER_TEMPERATURE, temp_error);
	}

	*error = error_check_fatal(temp_error, HAL_GetTick());
	ER_CHK(error);

End:;
}

/**
 * @brief		Wakes up all the devices connected to the isoSPI bus
 *
 * @param		hspi	The SPI configuration structure
 */
void _wakeup_idle(SPI_HandleTypeDef *hspi, bool apply_delay) {
	uint8_t data = 0xFF;
	HAL_GPIO_WritePin(CS_LTC_GPIO_Port, CS_LTC_Pin, GPIO_PIN_RESET);
	HAL_SPI_Transmit(hspi, &data, 1, 1);
	if (apply_delay) {
		HAL_Delay(1);
	}
	HAL_GPIO_WritePin(CS_LTC_GPIO_Port, CS_LTC_Pin, GPIO_PIN_SET);
}

/**
 * @brief		This function is used to calculate the PEC value
 *
 * @param		len		Length of the data array
 * @param		data	Array of data
 */
uint16_t _pec15(uint8_t len, uint8_t data[]) {
	uint16_t remainder, address;
	remainder = 16;  // PEC seed
	for (int i = 0; i < len; i++) {
		// calculate PEC table address
		address = ((remainder >> 7) ^ data[i]) & 0xff;
		remainder = (remainder << 8) ^ crcTable[address];
	}
	// The CRC15 has a 0 in the LSB so the final value must be multiplied by 2
	return (remainder * 2);
}

/**
 * @brief	This function is used to convert the 2 byte raw data from the
 * 				LTC68xx to a 16 bit unsigned integer
 *
 * @param 	v_data	Raw data bytes
 *
 * @retval	Voltage [mV]
 */
uint16_t _convert_voltage(uint8_t v_data[]) {
	return v_data[0] + (v_data[1] << 8);
}

/**
 * @brief		This function converts a voltage data from the zener sensor
 * 					to a temperature
 *
 * @param		volt	Voltage [mV]
 *
 * @retval	Temperature [C° * 100]
 */
uint16_t _convert_temp(uint16_t volt) {
	float voltf = volt * 0.0001;
	float temp;
	temp = -225.7 * voltf * voltf * voltf + 1310.6 * voltf * voltf -
		   2594.8 * voltf + 1767.8;
	return (uint16_t)(temp * 100);
}
