eagletrt/fenice-bms-hv-sw/mainboard/Src/can.c

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
/* Includes ------------------------------------------------------------------*/
#include "can.h"

/* USER CODE BEGIN 0 */

#define bms_IMPLEMENTATION
#define bms_IDS_IMPLEMENTATION
#define primary_IMPLEMENTATION
#define primary_IDS_IMPLEMENTATION

#include "can-bms.h"
#include "can-primary.h"

#undef bms_IMPLEMENTATION
#undef bms_IDS_IMPLEMENTATION
#undef primary_IMPLEMENTATION
#undef primary_IDS_IMPLEMENTATION

void MX_CAN1_Init_250K(void);
void MX_CAN1_Init_1M(void);

/* USER CODE END 0 */

CAN_HandleTypeDef hcan1;
CAN_HandleTypeDef hcan2;

/* CAN1 init function */
void MX_CAN1_Init(void) {
    hcan1.Instance                  = CAN1;
    hcan1.Init.Prescaler            = 3;
    hcan1.Init.Mode                 = CAN_MODE_NORMAL;
    hcan1.Init.SyncJumpWidth        = CAN_SJW_1TQ;
    hcan1.Init.TimeSeg1             = CAN_BS1_12TQ;
    hcan1.Init.TimeSeg2             = CAN_BS2_2TQ;
    hcan1.Init.TimeTriggeredMode    = DISABLE;
    hcan1.Init.AutoBusOff           = ENABLE;
    hcan1.Init.AutoWakeUp           = DISABLE;
    hcan1.Init.AutoRetransmission   = DISABLE;
    hcan1.Init.ReceiveFifoLocked    = DISABLE;
    hcan1.Init.TransmitFifoPriority = DISABLE;
    if (HAL_CAN_Init(&hcan1) != HAL_OK) {
        Error_Handler();
    }
}
/* CAN2 init function */
void MX_CAN2_Init(void) {
    hcan2.Instance                  = CAN2;
    hcan2.Init.Prescaler            = 3;
    hcan2.Init.Mode                 = CAN_MODE_NORMAL;
    hcan2.Init.SyncJumpWidth        = CAN_SJW_1TQ;
    hcan2.Init.TimeSeg1             = CAN_BS1_12TQ;
    hcan2.Init.TimeSeg2             = CAN_BS2_2TQ;
    hcan2.Init.TimeTriggeredMode    = DISABLE;
    hcan2.Init.AutoBusOff           = ENABLE;
    hcan2.Init.AutoWakeUp           = DISABLE;
    hcan2.Init.AutoRetransmission   = DISABLE;
    hcan2.Init.ReceiveFifoLocked    = DISABLE;
    hcan2.Init.TransmitFifoPriority = DISABLE;
    if (HAL_CAN_Init(&hcan2) != HAL_OK) {
        Error_Handler();
    }
}

static uint32_t HAL_RCC_CAN1_CLK_ENABLED = 0;

void HAL_CAN_MspInit(CAN_HandleTypeDef *canHandle) {
    GPIO_InitTypeDef GPIO_InitStruct = {0};
    if (canHandle->Instance == CAN1) {
        /* CAN1 clock enable */
        HAL_RCC_CAN1_CLK_ENABLED++;
        if (HAL_RCC_CAN1_CLK_ENABLED == 1) {
            __HAL_RCC_CAN1_CLK_ENABLE();
        }

        __HAL_RCC_GPIOA_CLK_ENABLE();
        /**CAN1 GPIO Configuration
    PA11     ------> CAN1_RX
    PA12     ------> CAN1_TX
    */
        GPIO_InitStruct.Pin       = CAN_CAR_RX_Pin | CAN_CAR_TX_Pin;
        GPIO_InitStruct.Mode      = GPIO_MODE_AF_PP;
        GPIO_InitStruct.Pull      = GPIO_NOPULL;
        GPIO_InitStruct.Speed     = GPIO_SPEED_FREQ_VERY_HIGH;
        GPIO_InitStruct.Alternate = GPIO_AF9_CAN1;
        HAL_GPIO_Init(GPIOA, &GPIO_InitStruct);

        /* CAN1 interrupt Init */
        HAL_NVIC_SetPriority(CAN1_RX0_IRQn, 0, 0);
        HAL_NVIC_EnableIRQ(CAN1_RX0_IRQn);
        HAL_NVIC_SetPriority(CAN1_RX1_IRQn, 0, 0);
        HAL_NVIC_EnableIRQ(CAN1_RX1_IRQn);
        HAL_NVIC_SetPriority(CAN1_SCE_IRQn, 0, 0);
        HAL_NVIC_EnableIRQ(CAN1_SCE_IRQn);
    } else if (canHandle->Instance == CAN2) {
        /* CAN2 clock enable */
        __HAL_RCC_CAN2_CLK_ENABLE();
        HAL_RCC_CAN1_CLK_ENABLED++;
        if (HAL_RCC_CAN1_CLK_ENABLED == 1) {
            __HAL_RCC_CAN1_CLK_ENABLE();
        }

        __HAL_RCC_GPIOB_CLK_ENABLE();
        /**CAN2 GPIO Configuration
    PB5     ------> CAN2_RX
    PB6     ------> CAN2_TX
    */
        GPIO_InitStruct.Pin       = CAN_CELL_RX_Pin | CAN_CELL_TX_Pin;
        GPIO_InitStruct.Mode      = GPIO_MODE_AF_PP;
        GPIO_InitStruct.Pull      = GPIO_NOPULL;
        GPIO_InitStruct.Speed     = GPIO_SPEED_FREQ_VERY_HIGH;
        GPIO_InitStruct.Alternate = GPIO_AF9_CAN2;
        HAL_GPIO_Init(GPIOB, &GPIO_InitStruct);

        /* CAN2 interrupt Init */
        HAL_NVIC_SetPriority(CAN2_RX0_IRQn, 0, 0);
        HAL_NVIC_EnableIRQ(CAN2_RX0_IRQn);
        HAL_NVIC_SetPriority(CAN2_RX1_IRQn, 0, 0);
        HAL_NVIC_EnableIRQ(CAN2_RX1_IRQn);
        HAL_NVIC_SetPriority(CAN2_SCE_IRQn, 0, 0);
        HAL_NVIC_EnableIRQ(CAN2_SCE_IRQn);
    }
}

void HAL_CAN_MspDeInit(CAN_HandleTypeDef *canHandle) {
    if (canHandle->Instance == CAN1) {
        /* Peripheral clock disable */
        HAL_RCC_CAN1_CLK_ENABLED--;
        if (HAL_RCC_CAN1_CLK_ENABLED == 0) {
            __HAL_RCC_CAN1_CLK_DISABLE();
        }

        /**CAN1 GPIO Configuration
    PA11     ------> CAN1_RX
    PA12     ------> CAN1_TX
    */
        HAL_GPIO_DeInit(GPIOA, CAN_CAR_RX_Pin | CAN_CAR_TX_Pin);

        /* CAN1 interrupt Deinit */
        HAL_NVIC_DisableIRQ(CAN1_RX0_IRQn);
        HAL_NVIC_DisableIRQ(CAN1_RX1_IRQn);
        HAL_NVIC_DisableIRQ(CAN1_SCE_IRQn);
    } else if (canHandle->Instance == CAN2) {
        /* Peripheral clock disable */
        __HAL_RCC_CAN2_CLK_DISABLE();
        HAL_RCC_CAN1_CLK_ENABLED--;
        if (HAL_RCC_CAN1_CLK_ENABLED == 0) {
            __HAL_RCC_CAN1_CLK_DISABLE();
        }

        /**CAN2 GPIO Configuration
    PB5     ------> CAN2_RX
    PB6     ------> CAN2_TX
    */
        HAL_GPIO_DeInit(GPIOB, CAN_CELL_RX_Pin | CAN_CELL_TX_Pin);

        /* CAN2 interrupt Deinit */
        HAL_NVIC_DisableIRQ(CAN2_RX0_IRQn);
        HAL_NVIC_DisableIRQ(CAN2_RX1_IRQn);
        HAL_NVIC_DisableIRQ(CAN2_SCE_IRQn);
    }
}

/* USER CODE BEGIN 1 */

void MX_CAN1_Init_250K(void) {
    hcan1.Instance                  = CAN1;
    hcan1.Init.Prescaler            = 10;
    hcan1.Init.Mode                 = CAN_MODE_NORMAL;
    hcan1.Init.SyncJumpWidth        = CAN_SJW_1TQ;
    hcan1.Init.TimeSeg1             = CAN_BS1_15TQ;
    hcan1.Init.TimeSeg2             = CAN_BS2_2TQ;
    hcan1.Init.TimeTriggeredMode    = DISABLE;
    hcan1.Init.AutoBusOff           = ENABLE;
    hcan1.Init.AutoWakeUp           = DISABLE;
    hcan1.Init.AutoRetransmission   = DISABLE;
    hcan1.Init.ReceiveFifoLocked    = DISABLE;
    hcan1.Init.TransmitFifoPriority = DISABLE;
    if (HAL_CAN_Init(&hcan1) != HAL_OK) {
        Error_Handler();
    }
}

void MX_CAN1_Init_1M(void) {
    hcan1.Instance                  = CAN1;
    hcan1.Init.Prescaler            = 3;
    hcan1.Init.Mode                 = CAN_MODE_NORMAL;
    hcan1.Init.SyncJumpWidth        = CAN_SJW_1TQ;
    hcan1.Init.TimeSeg1             = CAN_BS1_12TQ;
    hcan1.Init.TimeSeg2             = CAN_BS2_2TQ;
    hcan1.Init.TimeTriggeredMode    = DISABLE;
    hcan1.Init.AutoBusOff           = ENABLE;
    hcan1.Init.AutoWakeUp           = DISABLE;
    hcan1.Init.AutoRetransmission   = DISABLE;
    hcan1.Init.ReceiveFifoLocked    = DISABLE;
    hcan1.Init.TransmitFifoPriority = DISABLE;
    if (HAL_CAN_Init(&hcan1) != HAL_OK) {
        Error_Handler();
    }
}

/* USER CODE END 1 */
