eagletrt/fenice-bms-hv-sw/mainboard/Src/spi.c

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
/* Includes ------------------------------------------------------------------*/
#include "spi.h"

/* USER CODE BEGIN 0 */
void spi_enable_cs(SPI_HandleTypeDef *spi, GPIO_TypeDef *gpio, uint16_t pin) {
    HAL_GPIO_WritePin(gpio, pin, GPIO_PIN_RESET);
    while (spi->State != HAL_SPI_STATE_READY)
        ;
}

void spi_disable_cs(SPI_HandleTypeDef *spi, GPIO_TypeDef *gpio, uint16_t pin) {
    while (spi->State != HAL_SPI_STATE_READY)
        ;
    HAL_GPIO_WritePin(gpio, pin, GPIO_PIN_SET);
}
/* USER CODE END 0 */

SPI_HandleTypeDef hspi1;
SPI_HandleTypeDef hspi2;
SPI_HandleTypeDef hspi3;

/* SPI1 init function */
void MX_SPI1_Init(void)
{

  hspi1.Instance = SPI1;
  hspi1.Init.Mode = SPI_MODE_MASTER;
  hspi1.Init.Direction = SPI_DIRECTION_2LINES;
  hspi1.Init.DataSize = SPI_DATASIZE_8BIT;
  hspi1.Init.CLKPolarity = SPI_POLARITY_LOW;
  hspi1.Init.CLKPhase = SPI_PHASE_1EDGE;
  hspi1.Init.NSS = SPI_NSS_SOFT;
  hspi1.Init.BaudRatePrescaler = SPI_BAUDRATEPRESCALER_16;
  hspi1.Init.FirstBit = SPI_FIRSTBIT_MSB;
  hspi1.Init.TIMode = SPI_TIMODE_DISABLE;
  hspi1.Init.CRCCalculation = SPI_CRCCALCULATION_DISABLE;
  hspi1.Init.CRCPolynomial = 10;
  if (HAL_SPI_Init(&hspi1) != HAL_OK)
  {
    Error_Handler();
  }
}
/* SPI2 init function */
void MX_SPI2_Init(void)
{

  hspi2.Instance = SPI2;
  hspi2.Init.Mode = SPI_MODE_MASTER;
  hspi2.Init.Direction = SPI_DIRECTION_2LINES;
  hspi2.Init.DataSize = SPI_DATASIZE_8BIT;
  hspi2.Init.CLKPolarity = SPI_POLARITY_LOW;
  hspi2.Init.CLKPhase = SPI_PHASE_1EDGE;
  hspi2.Init.NSS = SPI_NSS_SOFT;
  hspi2.Init.BaudRatePrescaler = SPI_BAUDRATEPRESCALER_64;
  hspi2.Init.FirstBit = SPI_FIRSTBIT_MSB;
  hspi2.Init.TIMode = SPI_TIMODE_DISABLE;
  hspi2.Init.CRCCalculation = SPI_CRCCALCULATION_DISABLE;
  hspi2.Init.CRCPolynomial = 10;
  if (HAL_SPI_Init(&hspi2) != HAL_OK)
  {
    Error_Handler();
  }
}
/* SPI3 init function */
void MX_SPI3_Init(void)
{

  hspi3.Instance = SPI3;
  hspi3.Init.Mode = SPI_MODE_MASTER;
  hspi3.Init.Direction = SPI_DIRECTION_2LINES;
  hspi3.Init.DataSize = SPI_DATASIZE_8BIT;
  hspi3.Init.CLKPolarity = SPI_POLARITY_LOW;
  hspi3.Init.CLKPhase = SPI_PHASE_2EDGE;
  hspi3.Init.NSS = SPI_NSS_SOFT;
  hspi3.Init.BaudRatePrescaler = SPI_BAUDRATEPRESCALER_64;
  hspi3.Init.FirstBit = SPI_FIRSTBIT_MSB;
  hspi3.Init.TIMode = SPI_TIMODE_DISABLE;
  hspi3.Init.CRCCalculation = SPI_CRCCALCULATION_DISABLE;
  hspi3.Init.CRCPolynomial = 10;
  if (HAL_SPI_Init(&hspi3) != HAL_OK)
  {
    Error_Handler();
  }
}

void HAL_SPI_MspInit(SPI_HandleTypeDef* spiHandle)
{

  GPIO_InitTypeDef GPIO_InitStruct = {0};
  if(spiHandle->Instance==SPI1)
  {
    /* SPI1 clock enable */
    __HAL_RCC_SPI1_CLK_ENABLE();

    __HAL_RCC_GPIOA_CLK_ENABLE();
    /**SPI1 GPIO Configuration
    PA5     ------> SPI1_SCK
    PA6     ------> SPI1_MISO
    PA7     ------> SPI1_MOSI
    */
    GPIO_InitStruct.Pin = ADC_SCK_Pin|ADC_MISO_Pin|ADC_MOSI_Pin;
    GPIO_InitStruct.Mode = GPIO_MODE_AF_PP;
    GPIO_InitStruct.Pull = GPIO_NOPULL;
    GPIO_InitStruct.Speed = GPIO_SPEED_FREQ_VERY_HIGH;
    GPIO_InitStruct.Alternate = GPIO_AF5_SPI1;
    HAL_GPIO_Init(GPIOA, &GPIO_InitStruct);

  }
  else if(spiHandle->Instance==SPI2)
  {
    /* SPI2 clock enable */
    __HAL_RCC_SPI2_CLK_ENABLE();

    __HAL_RCC_GPIOB_CLK_ENABLE();
    /**SPI2 GPIO Configuration
    PB13     ------> SPI2_SCK
    PB14     ------> SPI2_MISO
    PB15     ------> SPI2_MOSI
    */
    GPIO_InitStruct.Pin = EEPROM_SCK_Pin|EEPROM_MISO_Pin|EEPROM_MOSI_Pin;
    GPIO_InitStruct.Mode = GPIO_MODE_AF_PP;
    GPIO_InitStruct.Pull = GPIO_NOPULL;
    GPIO_InitStruct.Speed = GPIO_SPEED_FREQ_VERY_HIGH;
    GPIO_InitStruct.Alternate = GPIO_AF5_SPI2;
    HAL_GPIO_Init(GPIOB, &GPIO_InitStruct);

  }
  else if(spiHandle->Instance==SPI3)
  {
    /* SPI3 clock enable */
    __HAL_RCC_SPI3_CLK_ENABLE();

    __HAL_RCC_GPIOC_CLK_ENABLE();
    __HAL_RCC_GPIOB_CLK_ENABLE();
    /**SPI3 GPIO Configuration
    PC11     ------> SPI3_MISO
    PC12     ------> SPI3_MOSI
    PB3     ------> SPI3_SCK
    */
    GPIO_InitStruct.Pin = MONITOR_MISO_Pin|MONITOR_MOSI_Pin;
    GPIO_InitStruct.Mode = GPIO_MODE_AF_PP;
    GPIO_InitStruct.Pull = GPIO_NOPULL;
    GPIO_InitStruct.Speed = GPIO_SPEED_FREQ_VERY_HIGH;
    GPIO_InitStruct.Alternate = GPIO_AF6_SPI3;
    HAL_GPIO_Init(GPIOC, &GPIO_InitStruct);

    GPIO_InitStruct.Pin = MONITOR_SCK_Pin;
    GPIO_InitStruct.Mode = GPIO_MODE_AF_PP;
    GPIO_InitStruct.Pull = GPIO_NOPULL;
    GPIO_InitStruct.Speed = GPIO_SPEED_FREQ_VERY_HIGH;
    GPIO_InitStruct.Alternate = GPIO_AF6_SPI3;
    HAL_GPIO_Init(MONITOR_SCK_GPIO_Port, &GPIO_InitStruct);

  }
}

void HAL_SPI_MspDeInit(SPI_HandleTypeDef* spiHandle)
{

  if(spiHandle->Instance==SPI1)
  {
    /* Peripheral clock disable */
    __HAL_RCC_SPI1_CLK_DISABLE();

    /**SPI1 GPIO Configuration
    PA5     ------> SPI1_SCK
    PA6     ------> SPI1_MISO
    PA7     ------> SPI1_MOSI
    */
    HAL_GPIO_DeInit(GPIOA, ADC_SCK_Pin|ADC_MISO_Pin|ADC_MOSI_Pin);

  }
  else if(spiHandle->Instance==SPI2)
  {
    /* Peripheral clock disable */
    __HAL_RCC_SPI2_CLK_DISABLE();

    /**SPI2 GPIO Configuration
    PB13     ------> SPI2_SCK
    PB14     ------> SPI2_MISO
    PB15     ------> SPI2_MOSI
    */
    HAL_GPIO_DeInit(GPIOB, EEPROM_SCK_Pin|EEPROM_MISO_Pin|EEPROM_MOSI_Pin);

  }
  else if(spiHandle->Instance==SPI3)
  {
    /* Peripheral clock disable */
    __HAL_RCC_SPI3_CLK_DISABLE();

    /**SPI3 GPIO Configuration
    PC11     ------> SPI3_MISO
    PC12     ------> SPI3_MOSI
    PB3     ------> SPI3_SCK
    */
    HAL_GPIO_DeInit(GPIOC, MONITOR_MISO_Pin|MONITOR_MOSI_Pin);

    HAL_GPIO_DeInit(MONITOR_SCK_GPIO_Port, MONITOR_SCK_Pin);

  }
}
