eagletrt/fenice-bms-hv-sw/cellboard/Core/Src/measurements.c

#include "measurements.h"

#include "temp.h"
#include "tim.h"
#include "volt.h"

measurements_flag_t flags;

uint8_t open_wire_check_status = 0;

void measurements_init(TIM_HandleTypeDef *htim) {
    __HAL_TIM_SetCompare(
        htim, VOLTS_START_CONVERTION_CHANNEL, TIM_MS_TO_TICKS(htim, VOLT_MEASURE_INTERVAL - VOLT_MEASURE_TIME));
    __HAL_TIM_SetCompare(htim, VOLTS_READ_CHANNEL, TIM_MS_TO_TICKS(htim, VOLT_MEASURE_INTERVAL));
    __HAL_TIM_SetCompare(htim, TEMPS_READ_CHANNEL, TIM_MS_TO_TICKS(htim, TEMP_MEASURE_INTERVAL));
    __HAL_TIM_CLEAR_IT(htim, TIM_IT_CC1);
    __HAL_TIM_CLEAR_IT(htim, TIM_IT_CC2);
    __HAL_TIM_CLEAR_IT(htim, TIM_IT_CC3);
    HAL_TIM_OC_Start_IT(htim, VOLTS_START_CONVERTION_CHANNEL);
    HAL_TIM_OC_Start_IT(htim, VOLTS_READ_CHANNEL);
    HAL_TIM_OC_Start_IT(htim, TEMPS_READ_CHANNEL);
    flags = 0;
}

void measurements_flags_check() {
    if (flags & MEASUREMENTS_VOLTS_START_CONVERTION_FLAG) {
        if (open_wire_check_status) {
            volt_start_open_wire_check(open_wire_check_status);
        } else {
            volt_start_measure();
        }
        flags &= ~MEASUREMENTS_VOLTS_START_CONVERTION_FLAG;
    }
    if (flags & MEASUREMENTS_VOLTS_READ_FLAG) {
        if (open_wire_check_status) {
            volt_read_open_wire(open_wire_check_status);
            if (open_wire_check_status == 4)
                volt_open_wire_check();
        } else {
            volt_read();
            can_send(CAN_BMS_MESSAGE_FRAME_ID_CELLBOARD_VOLTAGES);
            can_send(CAN_BMS_MESSAGE_FRAME_ID_CELLBOARD_VOLTAGES_INFO);
        }
        open_wire_check_status = (open_wire_check_status + 1) % 5;
        flags &= ~MEASUREMENTS_VOLTS_READ_FLAG;
    }
    if (flags & MEASUREMENTS_TEMPS_READ_FLAG) {
        temp_measure_all();
        can_send(CAN_BMS_MESSAGE_FRAME_ID_CELLBOARD_TEMPERATURES);
        can_send(CAN_BMS_MESSAGE_FRAME_ID_CELLBOARD_TEMPERATURES_INFO);
        can_send(CAN_BMS_MESSAGE_FRAME_ID_CELLBOARD_BOARD_STATUS);
        can_send(CAN_BMS_MESSAGE_FRAME_ID_CELLBOARD_VERSION);
        // can_send(0);
        flags &= ~MEASUREMENTS_TEMPS_READ_FLAG;
    }
}

void measurements_oc_handler(TIM_HandleTypeDef *htim) {
    uint32_t cnt = __HAL_TIM_GetCounter(htim);
    switch (htim->Channel) {
        case VOLTS_START_CONVERTION_ACTIVE_CHANNEL:
            flags |= MEASUREMENTS_VOLTS_START_CONVERTION_FLAG;
            break;

        case VOLTS_READ_ACTIVE_CHANNEL:
            __HAL_TIM_SetCompare(
                htim,
                VOLTS_START_CONVERTION_CHANNEL,
                cnt + TIM_MS_TO_TICKS(htim, VOLT_MEASURE_INTERVAL - VOLT_MEASURE_TIME));
            __HAL_TIM_SetCompare(
                htim, VOLTS_READ_CHANNEL, cnt + TIM_MS_TO_TICKS(htim, VOLT_MEASURE_INTERVAL + cellboard_index));
            flags |= MEASUREMENTS_VOLTS_READ_FLAG;
            break;

        case TEMPS_READ_ACTIVE_CHANNEL:
            __HAL_TIM_SetCompare(
                htim, TEMPS_READ_CHANNEL, cnt + TIM_MS_TO_TICKS(htim, TEMP_MEASURE_INTERVAL + cellboard_index));
            flags |= MEASUREMENTS_TEMPS_READ_FLAG;
            break;

        default:
            break;
    }
}
