eagletrt/fenice-bms-hv-sw/mainboard/Src/pack/cell_voltage.c

/**
 * @file cell_voltage.c
 * @brief Cells voltages management functions
 *
 * @date Apr 11, 2019
 * 
 * @author Matteo Bonora [matteo.bonora@studenti.unitn.it]
 * @author Antonio Gelain [antonio.gelain@studenti.unitn.it]
 */

#include "pack/cell_voltage.h"

#include <limits.h>
#include <string.h>

#include "max22530.h"
#include "mainboard_config.h"
#include "main.h"
#include "bms_fsm.h"
#include "error_simple.h"

cell_voltage cell_volts;

void cell_voltage_init() {
    memset(cell_volts.min, CELL_MAX_VOLTAGE, CELLBOARD_COUNT * sizeof(voltage_t));
    memset(cell_volts.max, 0, CELLBOARD_COUNT * sizeof(voltage_t));
    memset(cell_volts.avg, 0, CELLBOARD_COUNT * sizeof(float));
}
HAL_StatusTypeDef cell_voltage_set_cells(size_t cellboard_id,
    voltage_t min,
    voltage_t max,
    float avg) {

    cell_volts.min[cellboard_id] = min;
    cell_volts.max[cellboard_id] = max;
    cell_volts.avg[cellboard_id] = avg;
    
    return HAL_OK;
}

voltage_t cell_voltage_get_max() {
    voltage_t max = 0;
    for (size_t i = 0; i < CELLBOARD_COUNT; i++)
        max = MAX(max, cell_volts.max[i]);
    return max;
}
voltage_t cell_voltage_get_min() {
    voltage_t min = CELL_MAX_VOLTAGE;
    for (size_t i = 0; i < CELLBOARD_COUNT; i++)
        min = MIN(min, cell_volts.min[i]);
    return min;
}
float cell_voltage_get_sum() {
    return cell_voltage_get_avg() * PACK_CELL_COUNT;
}
float cell_voltage_get_avg() {
    float avg = 0;
    for (size_t i = 0; i < CELLBOARD_COUNT; i++)
        avg += cell_volts.avg[i];
    return avg / CELLBOARD_COUNT;
}

void cell_voltage_check_errors() {
    voltage_t min = cell_voltage_get_min();
    voltage_t max = cell_voltage_get_max();
    if (min < CELL_MIN_VOLTAGE) {
        error_simple_set(ERROR_GROUP_ERROR_CELL_UNDER_VOLTAGE, 0);
    } else {
        error_simple_reset(ERROR_GROUP_ERROR_CELL_UNDER_VOLTAGE, 0);
    }
    if (max > CELL_MAX_VOLTAGE) {
        error_simple_set(ERROR_GROUP_ERROR_CELL_OVER_VOLTAGE, 0);
    } else {
        error_simple_reset(ERROR_GROUP_ERROR_CELL_OVER_VOLTAGE, 0);
    }
}
