eagletrt/fenice-bms-hv-sw/mainboard/Src/imd.c

#include "imd.h"

#include <math.h>

#include "feedback.h"
#include "timer_utils.h"

uint32_t periodTicks = 0, dutyCycleTicks = 0;
uint32_t icValRising = 0, icValFalling = 0;

void imd_init() {
    __HAL_TIM_CLEAR_FLAG(&HTIM_IMD, TIM_IT_CC4);  //clears existing interrupts on channel 4
    HAL_TIM_IC_Start_IT(&HTIM_IMD, TIM_CHANNEL_4);
}

float imd_get_duty_cycle_percentage() {
    return imd_get_duty_cycle() * 100;
}

float imd_get_duty_cycle() {
    return periodTicks == 0 ? 0 : ((float)dutyCycleTicks / periodTicks);
}

uint8_t imd_get_freq() {
    return periodTicks == 0 ? 0 : roundf(1000.0 / TIM_TICKS_TO_MS(&HTIM_IMD, periodTicks));
}

uint8_t imd_get_period() {
    return roundf(TIM_TICKS_TO_MS(&HTIM_IMD, periodTicks));
}

uint8_t imd_is_fault() {
    return !feedback_is_ok(FEEDBACK_IMD_FAULT, FEEDBACK_IMD_FAULT);
}

IMD_STATE imd_get_state() {
    uint32_t freq = imd_get_freq();

    if (freq == 0)
        return IMD_SC;
    if (freq == 10)
        return IMD_NORMAL;
    if (freq == 20)
        return IMD_UNDER_VOLTAGE;
    if (freq == 30)
        return IMD_START_MEASURE;
    if (freq == 40)
        return IMD_DEVICE_ERROR;
    if (freq == 50)
        return IMD_EARTH_FAULT;

    return -1;
}

int32_t imd_get_details() {
    float duty = imd_get_duty_cycle_percentage();
    switch (imd_get_state()) {
        case IMD_SC:
            return !HAL_GPIO_ReadPin(
                IMD_PWM_GPIO_Port,
                IMD_PWM_Pin);  //assume that if isRisingEdge == 0 then the pin value is 1, otherwise 0
        case IMD_NORMAL:
        case IMD_UNDER_VOLTAGE:  //never reached
            return ((90 / (duty - 5)) - 1) * 1200;
        case IMD_START_MEASURE:
            if (duty < 15)
                return 1;
            else if (duty > 85)
                return 0;
            else
                return -1;
        case IMD_DEVICE_ERROR:
            if (duty < 55 && duty > 45)
                return 1;
            else
                return -1;
        case IMD_EARTH_FAULT:
            if (duty < 55 && duty > 45)
                return 1;
            else
                return -1;
        default:
            return -1;
    }
}

void HAL_TIM_IC_CaptureCallback(TIM_HandleTypeDef *htim) {
    if (htim->Instance == HTIM_IMD.Instance) {
        if (htim->Channel == HAL_TIM_ACTIVE_CHANNEL_4) {
            if (HAL_GPIO_ReadPin(IMD_PWM_GPIO_Port, IMD_PWM_Pin)) {
                uint32_t icValue = HAL_TIM_ReadCapturedValue(&HTIM_IMD, TIM_CHANNEL_4);

                periodTicks = icValue - icValRising;

                icValRising = icValue;
            } else {
                icValFalling = HAL_TIM_ReadCapturedValue(&HTIM_IMD, TIM_CHANNEL_4);

                dutyCycleTicks = icValFalling - icValRising;
            }
        }
    }
}
