eagletrt/fenice-bms-hv-sw/cellboard/Core/Src/volt.c

/**
 * @file		Volv.h
 * @brief		Voltage measurement functions
 *
 * @date		Jul 17, 2021
 * @author		Matteo Bonora [matteo.bonora@studenti.unitn.it]
 */

#include "volt.h"

#include "spi.h"


voltage_t voltages[CELLBOARD_CELL_COUNT] = { 0 };

voltage_t voltages_pup[CELLBOARD_CELL_COUNT] = { 0 };
voltage_t voltages_pud[CELLBOARD_CELL_COUNT] = { 0 };

void volt_init() {
    // Set initial voltage to an in range value
    for (size_t i = 0; i < CELLBOARD_CELL_COUNT; i++) {
        voltages[i] = 33000;
        voltages_pud[i] = 33000;
        voltages_pup[i] = 33000;
    }
}

void volt_start_measure() {
    ltc6813_adcv(&LTC6813_SPI);
}

void volt_read() {
    ltc6813_read_voltages(&LTC6813_SPI, voltages);
}

void volt_start_open_wire_check(uint8_t status) {
    ltc6813_adow(&LTC6813_SPI, status > 2 ? LTC6813_ADOW_PUP_INACTIVE : LTC6813_ADOW_PUP_ACTIVE);
}

void volt_read_open_wire(uint8_t status) {
    ltc6813_read_voltages(&LTC6813_SPI, status > 2 ? voltages_pud : voltages_pup);
}

void volt_open_wire_check() {
    for(uint8_t i = 1; i < CELLBOARD_CELL_COUNT; ++i) {
        int32_t diff = (int32_t)voltages_pup[i] - voltages_pud[i];

        if(diff < -4000) {
            ERROR_SET(ERROR_OPEN_WIRE);
            return;
        }
    }

    if(voltages_pup[0] == 0){
        ERROR_SET(ERROR_OPEN_WIRE);
        return;
    }
    if(voltages_pud[17] == 0){
        ERROR_SET(ERROR_OPEN_WIRE);
        return;
    }

    ERROR_UNSET(ERROR_OPEN_WIRE);
}

voltage_t volt_get_min() {
    voltage_t min = CELL_MAX_VOLTAGE;
    for (size_t i = 0; i < CELLBOARD_CELL_COUNT; i++)
        min = MIN(min, voltages[i]);
    return min;
}
voltage_t volt_get_max() {
    voltage_t max = 0;
    for (size_t i = 0; i < CELLBOARD_CELL_COUNT; i++)
        max = MAX(max, voltages[i]);
    return max;
}
float volt_get_avg() {
    float avg = 0;
    for (size_t i = 0; i < CELLBOARD_CELL_COUNT; i++)
        avg += voltages[i];
    return avg / CELLBOARD_CELL_COUNT;
}

uint16_t volt_get_min_index() {
    uint16_t min = 0;
    for (uint16_t i = 0; i < CELLBOARD_CELL_COUNT; i++) {
        if (voltages[i] < voltages[min]) {
            min = i;
        }
    }
    return min;
}

voltage_t * volt_get_volts() {
    return voltages;
}
